marcosindiano7/ESP32-Temperature-WebServer-PCB/docs/images/web-interface-alert.jpeg

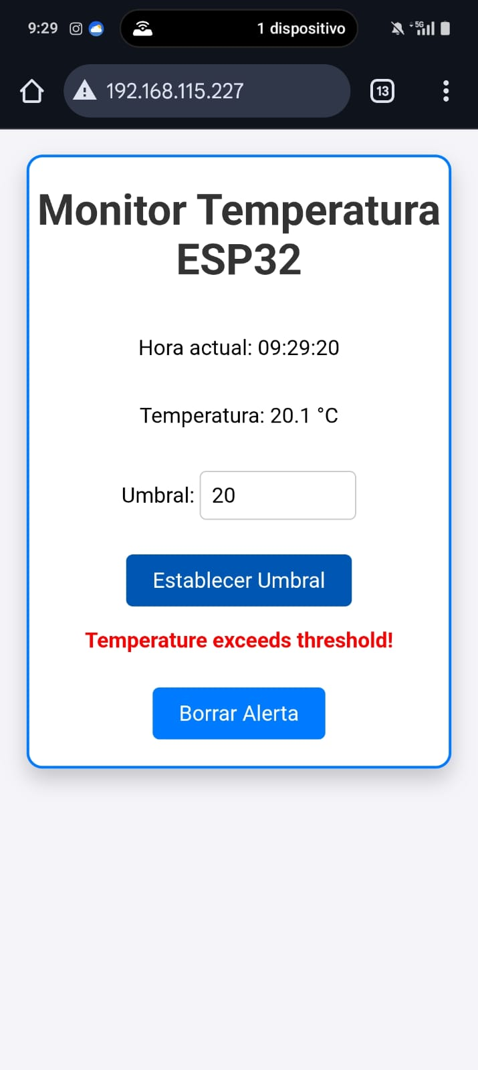
docs/images/web-interface-alert.jpeg
